shannon-greenlight/spankulator/Spankulator-Code/arduino_bin/Assets/app.150x150.png

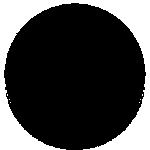
Spankulator-Code/arduino_bin/Assets/app.150x150.png
