shannon-greenlight/spankulator/Spankulator-Code/arduino_bin/Assets/arduino.150x150.png

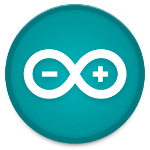
Spankulator-Code/arduino_bin/Assets/arduino.150x150.png
