shannon-greenlight/spankulator/Spankulator-Hardware/spice/spank_output.asc

C1: cap; 0.01µ; V=200 Irms=0 Rser=0 Lser=0 mfg="Murata" pn="GRM31CR72D104KW03" type="X7R"
R3: res; 100K
R4: res; 100K
R5: res; 323.32K
U1: AD820
V1: voltage; 12
V2: voltage; 1.65
V3: signal; SINE(1.65 1.65 3000 0 0); AC 1
V4: voltage; 12
Named nets: 0, V+, V-, Vout
.tran 0 .01 0 .001
