shannon-greenlight/spankulator/Spankulator-Hardware/spice/anti_alias_5k-2.asc

C1: cap; 3nF
C2: cap; 82nF
C3: cap; 8.2nF
C4: cap; 82nF
C5: cap; 8.2nF
C6: cap; 82nF
C7: cap; 8.2nF
C8: cap; 82nF
R1: res; 4990
R2: res; 4990
R3: res; 953
R4: res; 9760
R5: res; 604
R6: res; 1540
R7: res; 1870
R8: res; 511
U1: AD820
U2: AD820
U3: AD820
U4: AD820
V1: voltage; 12
V3: signal; SINE(0 2 2000 0 0); AC 1
V4: voltage; 12
Named nets: V+, V-, 0
;tran 0 .01 0 .001
.ac oct 10 100 10000
