shannon-greenlight/spankulator/Spankulator-Hardware/spice/anti_alias_5k.asc

C1: cap; 10nF
C2: cap; 10.5nF
C3: cap; 10nF
C4: cap; 14.7nF
C5: cap; 10nF
C6: cap; 33.2nF
C7: cap; 10nF
C8: cap; 274nF
R1: res; 6980
R2: res; 8660
R3: res; 5760
R4: res; 7500
R5: res; 3740
R6: res; 5110
R7: res; 1870
R8: res; 1240
U1: AD820
U2: AD820
U3: AD820
U4: AD820
V1: voltage; 12
V3: signal; SINE(0 2 2000 0 0); AC 1
V4: voltage; 12
Named nets: V+, V-, 0
;tran 0 .01 0 .001
.ac oct 10 100 5000
