shannon-greenlight/spankulator/Spankulator-Hardware/spice/Draft1.asc

C1: cap; 100nF
R1: res; 1K
V1: signal
Named nets: Input, Output, 0
.ac oct 20 10 2000
