shannon-greenlight/spankulator/Spankulator-Hardware/spice/op_int_rc.asc

C1: cap; 100nF
C2: cap; .01µF
R1: res; 100K
R2: res; 200K
R3: res; 10K
U1: AD744
V1: signal; AC 1
V2: voltage; 12
V3: voltage; 12
Named nets: Input, Output, 0, +12V, -12V, Out2
.ac oct 10 1 10000
