shannon-greenlight/spankulator/Spankulator-Hardware/spice/rc.asc

C1: cap; 10nF
R1: res; 1K
V1: signal; AC 1
Named nets: Input, Output, 0
.ac oct 20 1000 200000
