shannon-greenlight/spankulator/Spankulator-Hardware/spice/spank_dig_output.asc

C1: cap; .1µF
C2: cap; .1µF
D1: schottky
D2: schottky
Q1: npn; 2N3904
Q2: pnp; 2N3906
R1: res; 100
R2: res; 47K
R3: res; 1000
R4: res; 100K
V1: voltage; 2.5
V2: voltage; 5
V3: signal; PULSE(0 3.3 1 .0001 .0001 .1 .2); AC 1
Named nets: 0, Vin, Vout
.tran 0 11 10 .1
.MODEL MyBJT AKO: 2N3904 (Bf=430)
