shannon-greenlight/spankulator/Spankulator-Hardware/spice/spank_dig_output_2fet.asc

D1: schottky
D2: schottky
M1: nmos; IRF2204
Q1: npn; 2N3904
Q2: pnp
R1: res; 470
R2: res; 0
R3: res; 47K
R4: res; 1000K
R5: res; 10K
R6: res; 0
R7: res; 47K
V2: voltage; 5
V3: signal; PULSE(0 3.3 0 .0001 .0001 .001 .002); AC 1
Named nets: 0, Vin, Vout
.tran 0 10.003 10 .0001
