shannon-greenlight/spankulator/Spankulator-Hardware/spice/spank_dig_output_fet.asc

D1: schottky
D2: schottky
M1: nmos; RJK0305DPB
R1: res; 470
R3: res; 470
R4: res; 10K
V2: voltage; 5
V3: signal; PULSE(0 3.3 1 .0001 .0001 .1 .2); AC 1
Named nets: 0, Vin, Vout
.tran 0 11 10 .1
