shannon-greenlight/spankulator/Spankulator-Hardware/spice/spank_input.asc

C1: cap; 1µF
C2: cap; .0047µF
C3: cap; 156pF
D1: diode
D2: diode
D3: diode
D4: diode
R1: res; 300K
R2: res; 100K
R3: res; 470
R4: res; 300K
R5: res; 470
R6: res; 10K
R7: res; 10K
R8: res; 100K
R9: res; 300K
U1: AD820
U2: AD820
V1: voltage; 12
V2: voltage; 3.3
V3: signal; SINE(0 5 2000 0 0); AC 1
V4: voltage; 12
Named nets: 0, V+, V-, Vout, Vac, 3.3V, Vin
.tran 0 .01 0 .001
