shannon-greenlight/spankulator/Spankulator-Hardware/spice/spank_input_new.asc

C1: cap; 1µF
D1: diode
D2: diode
D3: diode
D4: diode
R1: res; 300.3K; tol=.1
R2: res; 99.9K; tol=.1
R3: res; 100K
R4: res; 100.1K; tol=.1
R6: res; 10K
R7: res; 10K
R8: res; 100K
R9: res; 300K
U1: AD820
U2: AD820
V1: voltage; 12
V2: voltage; 3.3
V3: signal; SINE(0 5 100 0 0); AC 1
V4: voltage; 12
V5: voltage; 1.65
Named nets: 0, V+, V-, Vout, Vac, 3.3V, Vin, -1.65V
.tran 0 .01 0 .001
