shannon-greenlight/spankulator/Spankulator-Hardware/spice/spank_output_analog.asc

R1: res; 100K
R2: res; 301K
R3: res; 100K
R4: res; 66.5K
R5: res; 100K
R6: res; 200K
R7: res; 100K
U1: AD820
U2: AD820
U3: AD820
V1: voltage; 12
V2: voltage; 3.3
V3: signal; SINE(1.65 1.65 3 0 0); AC 1
V4: voltage; 12
Named nets: 0, V+, V-, Vout, V2
.tran 0 11 10 .1
