shannon-greenlight/spankulator/Spankulator-Hardware/spice/spank_output_analog2.asc

R1: res; 100K
R2: res; 324K
R8: res; 100K
U2: AD820
V1: voltage; 12
V3: signal; SINE(1.65 1.65 3 0 0); AC 1
V4: voltage; 12
V5: voltage; 1.65
Named nets: V+, V-, 0, Vout
.tran 0 11 10 .1
